DPIclimate/kangaroo-node/firmware/include/davis.h

#ifndef DAVIS_ANEMOMETER_H
#define DAVIS_ANEMOMETER_H

#include <Arduino.h>

static volatile uint32_t wind_count = 0;

void davis_isr() {
    wind_count++;
}

class Davis {
private:
    int _directionPin;
    int _speedPin;

public:
    Davis(int directionPin, int speedPin) : _directionPin { directionPin}, _speedPin { speedPin } {
        pinMode(_directionPin, INPUT);
        pinMode(_speedPin, INPUT);
    }

    uint32_t getDirectionRaw() {
        return analogRead(_directionPin);
    }

    float getDirectionDegrees(uint32_t dir) {
        static const float a2dFactor = 360.0f / 1024.0f;
        return dir * a2dFactor;
    }

    void startSpeedMeasurement() {
        wind_count = 0;
        // The Davis anemometer holds the speed line high, and pulses it low to show a revolution.
        attachInterrupt(digitalPinToInterrupt(_speedPin), davis_isr, FALLING);
    }

    uint32_t stopSpeedMeasurement() {
        detachInterrupt(_speedPin);
        return wind_count;
    }

    float getSpeedMph(const uint32_t count, const uint32_t s) {
        // convert to mp/h using the formula V=P(2.25/T)
        return count * 2.25 / s;
    }

    float getSpeedKph(const uint32_t count, const uint32_t ms) {
        return getSpeedMph(count, ms) * 1.60934;
    }
};

#endif // DAVIS_ANEMOMETER_H
